SHIMA-R7/fc-magicon/firmware/magicon/menu_driver.h

// gen_menu_driver.py が作ったゲーム選択メニュー($C000- のプログラム・画面の土台)。手で直さない
#pragma once
#include <stdint.h>

#define MENUD_COUNT        0x0000
#define MENUD_PTR_LO       0x0100
#define MENUD_PTR_HI       0x0180
#define MENUD_TITLES       0x0200
#define MENUD_TITLE_ADDR   0x8200
#define MENUD_TITLE_LEN    0x001C
#define MENUD_NT           0x1800
#define MENUD_CODE         0x4000
#define MENUD_SELECT       0x5FF0
#define MENUD_MAX_ITEMS    0x007F

//   $0300: 78                       SEI
//   $0301: A9 00                    LDA #$00
//   $0303: 8D 00 20                 STA $2000
//   $0306: 8D 01 20                 STA $2001
//   $0309: 8D 15 40                 STA $4015
//   $030C: A5 00                    LDA $00
//   $030E: 8D F0 5F                 STA $5FF0
//   $0311: A2 5A                    LDX #$5A
// w:
//   $0313: 2C 02 20                 BIT $2002
//   $0316: 10 FB                    BPL w
//   $0318: CA                       DEX
//   $0319: D0 F8                    BNE w
//   $031B: A9 00                    LDA #$00
//   $031D: AA                       TAX
// c:
//   $031E: 9D 00 00                 STA $0000,X
//   $0321: 9D 00 01                 STA $0100,X
//   $0324: 9D 00 02                 STA $0200,X
//   $0327: 9D 00 04                 STA $0400,X
//   $032A: 9D 00 05                 STA $0500,X
//   $032D: 9D 00 06                 STA $0600,X
//   $0330: 9D 00 07                 STA $0700,X
//   $0333: E8                       INX
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
    0x20, 0x20, 0x20, 0x20, 0x20, 0x20, 0x20, 0x20, 0x20, 0x20, 0x20, 0x20, 0x20, 0x20, 0x20, 0x20,
    0x20, 0x20, 0x20, 0x20, 0x20, 0x20, 0x20, 0x20, 0x20, 0x20, 0x20, 0x20, 0x20, 0x20, 0x20, 0x20,
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
};
