SHIMA-R7/fc-magicon/firmware/magicon/remote_driver.h

// gen_remote_driver.py が作った画面転送モードの 6502 プログラム($C000-、16KB)とカーソルの CHR。手で直さない
#pragma once
#include <stdint.h>

#define RD_PAL     0x5D00
#define RD_ATTR    0x5D20
#define RD_OAM     0x5E00
#define RD_IO      0x5F00

// reset:
//   $C000: 78                       SEI
//   $C001: D8                       CLD
//   $C002: A2 FF                    LDX #$FF
//   $C004: 9A                       TXS
//   $C005: A9 00                    LDA #$00
//   $C007: 8D 00 20                 STA $2000
//   $C00A: 8D 01 20                 STA $2001
//   $C00D: 8D 10 40                 STA $4010
//   $C010: A9 40                    LDA #$40
//   $C012: 8D 17 40                 STA $4017
// vbl1:
//   $C015: 2C 02 20                 BIT $2002
//   $C018: 10 FB                    BPL vbl1
// vbl2:
//   $C01A: 2C 02 20                 BIT $2002
//   $C01D: 10 FB                    BPL vbl2
//   $C01F: A9 3F                    LDA #$3F
//   $C021: 8D 06 20                 STA $2006
//   $C024: A9 00                    LDA #$00
//   $C026: 8D 06 20                 STA $2006
//   $C029: A2 00                    LDX #$00
// pal:
//   $C02B: BD 00 5D                 LDA $5D00,X
//   $C02E: 8D 07 20                 STA $2007
//   $C031: E8                       INX
//   $C032: E0 20                    CPX #$20
//   $C034: D0 F5                    BNE pal
//   $C036: A9 20                    LDA #$20
//   $C038: 8D 06 20                 STA $2006
//   $C03B: A9 00                    LDA #$00
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
    0x07, 0x20, 0xAD, 0x46, 0x5D, 0x8D, 0x07, 0x20, 0xAD, 0x47, 0x5D, 0x8D, 0x07, 0x20, 0xAD, 0x48,
    0x5D, 0x8D, 0x07, 0x20, 0xAD, 0x49, 0x5D, 0x8D, 0x07, 0x20, 0xAD, 0x4A, 0x5D, 0x8D, 0x07, 0x20,
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
};
static const uint8_t remote_spr_chr[64] = {
    0x80, 0xC0, 0xE0, 0xF0, 0xF8, 0xFC, 0xFE, 0xFF, 0x80, 0xC0, 0xA0, 0x90, 0x88, 0x84, 0x82, 0x81,
    0x00, 0x00, 0x00, 0x00, 0x00, 0x00, 0x00, 0x00, 0x00, 0x00, 0x00, 0x00, 0x00, 0x00, 0x00, 0x00,
    0xFF, 0xFF, 0xFF, 0xFE, 0xEF, 0xCF, 0x87, 0x07, 0x80, 0x80, 0x83, 0x92, 0xA9, 0xC9, 0x84, 0x07,
    0x80, 0xC0, 0xE0, 0x00, 0x00, 0x00, 0x80, 0x80, 0x80, 0x40, 0xE0, 0x00, 0x00, 0x00, 0x80, 0x80,
};
