SHIMA-R7/fc-magicon/firmware/magicon/nsf_driver.h

// gen_nsf_driver.py が作った NSF プレイヤーのドライバー($5000-)・画面の土台・CHR。手で直さない
#pragma once
#include <stdint.h>

#define NSFD_BASE            0x5000
#define NSFD_NT              0x0800
#define NSFD_PARAM           0x0F00
#define NSFD_RESET           0x5000
#define NSFD_NMI             0x519A
#define NSFD_IRQ             0x5288
#define NSFD_INIT_OPERAND    0x028A
#define NSFD_PLAY_OPERAND    0x028D
#define NSFD_ROW_TITLE       0x0009
#define NSFD_ROW_ARTIST      0x000B
#define NSFD_ROW_COPY        0x000D

// reset:
//   $5000: 78                       SEI
//   $5001: D8                       CLD
//   $5002: A2 FF                    LDX #$FF
//   $5004: 9A                       TXS
//   $5005: A9 00                    LDA #$00
//   $5007: 8D 00 20                 STA $2000
//   $500A: 8D 01 20                 STA $2001
//   $500D: 8D 15 40                 STA $4015
// vbl1:
//   $5010: 2C 02 20                 BIT $2002
//   $5013: 10 FB                    BPL vbl1
// vbl2:
//   $5015: 2C 02 20                 BIT $2002
//   $5018: 10 FB                    BPL vbl2
//   $501A: A9 3F                    LDA #$3F
//   $501C: 8D 06 20                 STA $2006
//   $501F: A9 00                    LDA #$00
//   $5021: 8D 06 20                 STA $2006
//   $5024: A2 00                    LDX #$00
// pal:
//   $5026: BD 8F 52                 LDA paltab,X
//   $5029: 8D 07 20                 STA $2007
//   $502C: E8                       INX
//   $502D: E0 20                    CPX #$20
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
    0x38, 0x28, 0x30, 0x7C, 0x58, 0x3C, 0x00, 0x00, 0x00, 0x00, 0x00, 0x00, 0x00, 0x00, 0x00, 0x00,
    0x08, 0x08, 0x00, 0x00, 0x00, 0x00, 0x00, 0x00, 0x00, 0x00, 0x00, 0x00, 0x00, 0x00, 0x00, 0x00,
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
};
