SHIMA-R7/fc-magicon/firmware/chr_test/chr_rom.h

// gen_chr_rom.py が作った 16KB のテスト ROM($8000 と $C000 に鏡映)
// reset:
//   $C000: 78                       SEI
//   $C001: D8                       CLD
//   $C002: A2 FF                    LDX #$FF
//   $C004: 9A                       TXS
//   $C005: A9 00                    LDA #$00
//   $C007: 8D 00 20                 STA $2000
//   $C00A: 8D 01 20                 STA $2001
// vbl1:
//   $C00D: 2C 02 20                 BIT $2002
//   $C010: 10 FB                    BPL vbl1
// vbl2:
//   $C012: 2C 02 20                 BIT $2002
//   $C015: 10 FB                    BPL vbl2
//   $C017: A9 3F                    LDA #$3F
//   $C019: 8D 06 20                 STA $2006
//   $C01C: A9 00                    LDA #$00
//   $C01E: 8D 06 20                 STA $2006
//   $C021: A2 00                    LDX #$00
// pal:
//   $C023: BD 7B C0                 LDA paltab,X
//   $C026: 8D 07 20                 STA $2007
//   $C029: E8                       INX
//   $C02A: E0 10                    CPX #$10
//   $C02C: D0 F5                    BNE pal
//   $C02E: A9 20                    LDA #$20
//   $C030: 8D 06 20                 STA $2006
//   $C033: A9 00                    LDA #$00
//   $C035: 8D 06 20                 STA $2006
//   $C038: A0 04                    LDY #$04
//   $C03A: A2 00                    LDX #$00
// nt:
//   $C03C: 8E 07 20                 STX $2007
//   $C03F: E8                       INX
//   $C040: D0 FA                    BNE nt
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
    0xEA, 0xEA, 0xEA, 0xEA, 0xEA, 0xEA, 0xEA, 0xEA, 0xEA, 0xEA, 0xEA, 0xEA, 0xEA, 0xEA, 0xEA, 0xEA,
    0xEA, 0xEA, 0xEA, 0xEA, 0xEA, 0xEA, 0xEA, 0xEA, 0xEA, 0xEA, 0xEA, 0xEA, 0xEA, 0xEA, 0xEA, 0xEA,
    0xEA, 0xEA, 0xEA, 0xEA, 0xEA, 0xEA, 0xEA, 0xEA, 0xEA, 0xEA, 0xEA, 0xEA, 0xEA, 0xEA, 0xEA, 0xEA,
    0xEA, 0xEA, 0xEA, 0xEA, 0xEA, 0xEA, 0xEA, 0xEA, 0xEA, 0xEA, 0xEA, 0xEA, 0xEA, 0xEA, 0xEA, 0xEA,
    0xEA, 0xEA, 0xEA, 0xEA, 0xEA, 0xEA, 0xEA, 0xEA, 0xEA, 0xEA, 0xEA, 0xEA, 0xEA, 0xEA, 0xEA, 0xEA,
    0xEA, 0xEA, 0xEA, 0xEA, 0xEA, 0xEA, 0xEA, 0xEA, 0xEA, 0xEA, 0xEA, 0xEA, 0xEA, 0xEA, 0xEA, 0xEA,
    0xEA, 0xEA, 0xEA, 0xEA, 0xEA, 0xEA, 0xEA, 0xEA, 0xEA, 0xEA, 0xEA, 0xEA, 0xEA, 0xEA, 0xEA, 0xEA,
    0xEA, 0xEA, 0xEA, 0xEA, 0xEA, 0xEA, 0xEA, 0xEA, 0xEA, 0xEA, 0xEA, 0xEA, 0xEA, 0xEA, 0xEA, 0xEA,
    0xEA, 0xEA, 0xEA, 0xEA, 0xEA, 0xEA, 0xEA, 0xEA, 0xEA, 0xEA, 0xEA, 0xEA, 0xEA, 0xEA, 0xEA, 0xEA,
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
};
