SHIMA-R7/fc-magicon/firmware/bus_test/test_rom.h

// gen_test_rom.py が作った 16KB のテスト ROM。$8000 と $C000 に鏡映して返す
// $C000: 78        SEI
// $C001: D8        CLD
// $C002: A2 FF     LDX #$FF
// $C004: 9A        TXS
// $C005: A9 00     LDA #$00
// $C007: 8D 00 20  STA $2000   ; NMI・PPU 設定を切る
// $C00A: 8D 01 20  STA $2001   ; 表示を止める
// $C00D: A9 01     LDA #$01
// $C00F: 8D 15 40  STA $4015   ; 矩形波 1ch だけ有効
// $C012: A9 BF     LDA #$BF
// $C014: 8D 00 40  STA $4000   ; デューティ50%・長さ停止・固定音量15
// $C017: A9 08     LDA #$08
// $C019: 8D 01 40  STA $4001   ; スイープ無効
// $C01C: A9 FD     LDA #$FD
// $C01E: 8D 02 40  STA $4002   ; 周期 下位 ($0FD → 1789773/16/254 ≈ 440Hz)
// $C021: A9 00     LDA #$00
// $C023: 8D 03 40  STA $4003   ; 周期 上位・長さ
// $C026: E6 00     INC $00
// $C028: A5 00     LDA $00
// $C02A: 8D 00 80  STA $8000   ; カセットへ書く(RP2350B が数える)
// $C02D: 4C 26 C0  JMP loop
// $C030: 40        RTI
static const unsigned char test_rom[16384] = {
    0x78, 0xD8, 0xA2, 0xFF, 0x9A, 0xA9, 0x00, 0x8D, 0x00, 0x20, 0x8D, 0x01, 0x20, 0xA9, 0x01, 0x8D,
    0x15, 0x40, 0xA9, 0xBF, 0x8D, 0x00, 0x40, 0xA9, 0x08, 0x8D, 0x01, 0x40, 0xA9, 0xFD, 0x8D, 0x02,
    0x40, 0xA9, 0x00, 0x8D, 0x03, 0x40, 0xE6, 0x00, 0xA5, 0x00, 0x8D, 0x00, 0x80, 0x4C, 0x26, 0xC0,
    0x40, 0xEA, 0xEA, 0xEA, 0xEA, 0xEA, 0xEA, 0xEA, 0xEA, 0xEA, 0xEA, 0xEA, 0xEA, 0xEA, 0xEA, 0xEA,
    0xEA, 0xEA, 0xEA, 0xEA, 0xEA, 0xEA, 0xEA, 0xEA, 0xEA, 0xEA, 0xEA, 0xEA, 0xEA, 0xEA, 0xEA, 0xEA,
    0xEA, 0xEA, 0xEA, 0xEA, 0xEA, 0xEA, 0xEA, 0xEA, 0xEA, 0xEA, 0xEA, 0xEA, 0xEA, 0xEA, 0xEA, 0xEA,
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
    0xEA, 0xEA, 0xEA, 0xEA, 0xEA, 0xEA, 0xEA, 0xEA, 0xEA, 0xEA, 0xEA, 0xEA, 0xEA, 0xEA, 0xEA, 0xEA,
    0xEA, 0xEA, 0xEA, 0xEA, 0xEA, 0xEA, 0xEA, 0xEA, 0xEA, 0xEA, 0xEA, 0xEA, 0xEA, 0xEA, 0xEA, 0xEA,
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
};
